proyectoitsv/2025_EWHRA/Diseño/Maqueta PMV/Dispositivo EWHRA (Conjunto).jpg

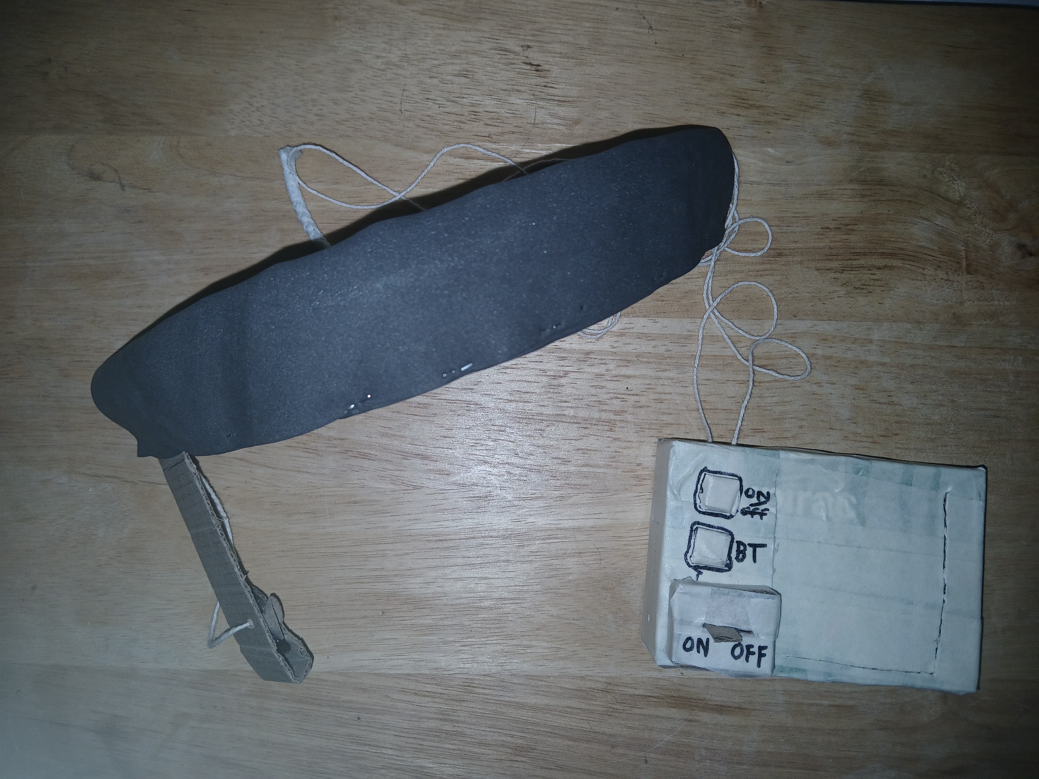
Diseño/Maqueta PMV/Dispositivo EWHRA (Conjunto).jpg
