proyectoitsv/2025_EWHRA/Diseño/Maqueta PMV/Usuario con EWHRA (Perfil).jpg

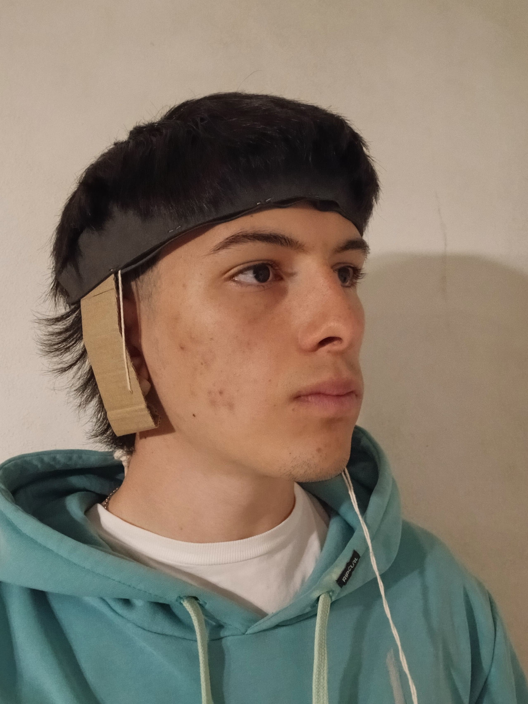
Diseño/Maqueta PMV/Usuario con EWHRA (Perfil).jpg
