proyectoitsv/2025_EWHRA/Diseño/Prototipo PMV/EWHRA_PMV.jpg

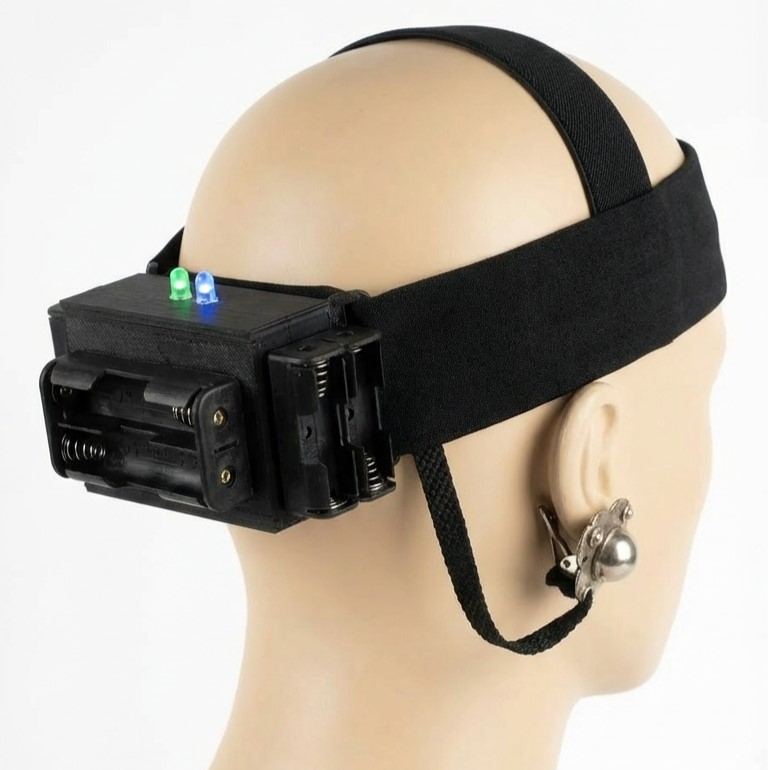
Diseño/Prototipo PMV/EWHRA_PMV.jpg
