proyectoitsv/2025_EWHRA/Diseño/Referencias/1.Alimentacion.png

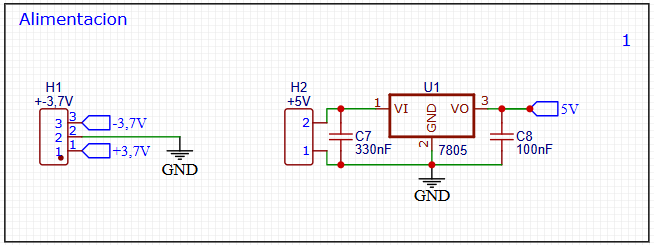
Diseño/Referencias/1.Alimentacion.png
