proyectoitsv/2025_EWHRA/Diseño/Referencias/3.Filtro_pasabanda.png

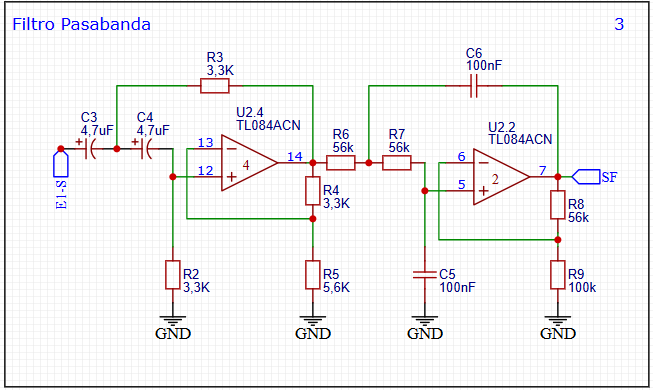
Diseño/Referencias/3.Filtro_pasabanda.png
