proyectoitsv/2025_EWHRA/Diseño/Referencias/4.Amplificador.png

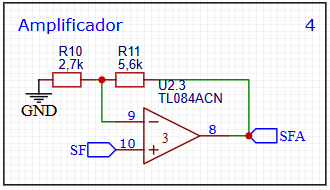
Diseño/Referencias/4.Amplificador.png
