proyectoitsv/2025_EWHRA/Diseño/Referencias/5.Amplificacion_INA.png

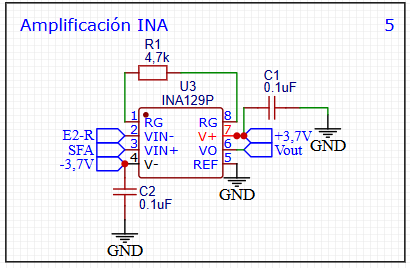
Diseño/Referencias/5.Amplificacion_INA.png
