proyectoitsv/2025_EWHRA/Diseño/Referencias/6.Microcontrolador.png

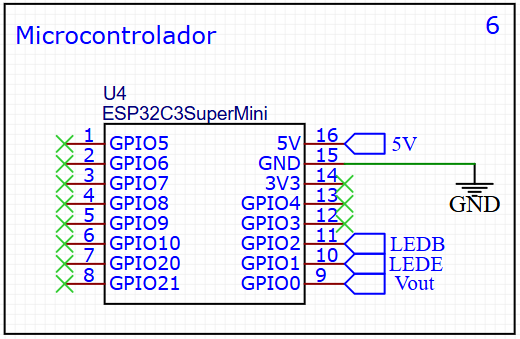
Diseño/Referencias/6.Microcontrolador.png
