proyectoitsv/2025_EWHRA/Interfaz Gráfica/Screenshots/AppEWHRA_Conectado.jpg

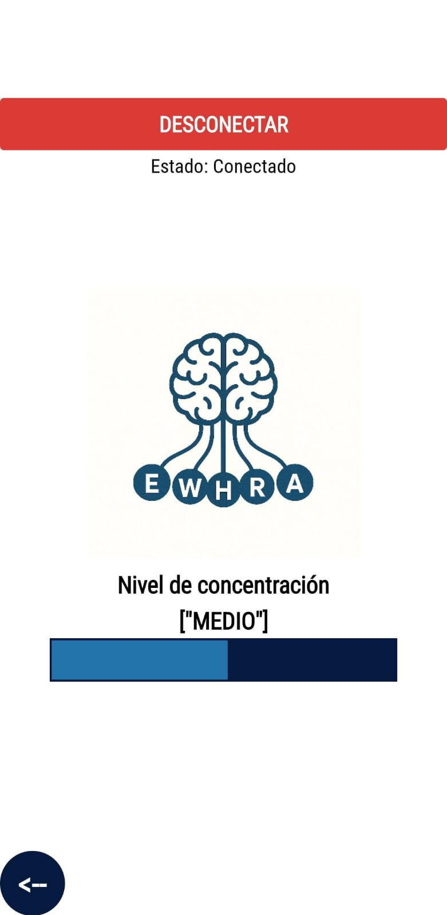
Interfaz Gráfica/Screenshots/AppEWHRA_Conectado.jpg
