proyectoitsv/2025_EWHRA/Interfaz Gráfica/Screenshots/AppEWHRA_Desconectado.jpg

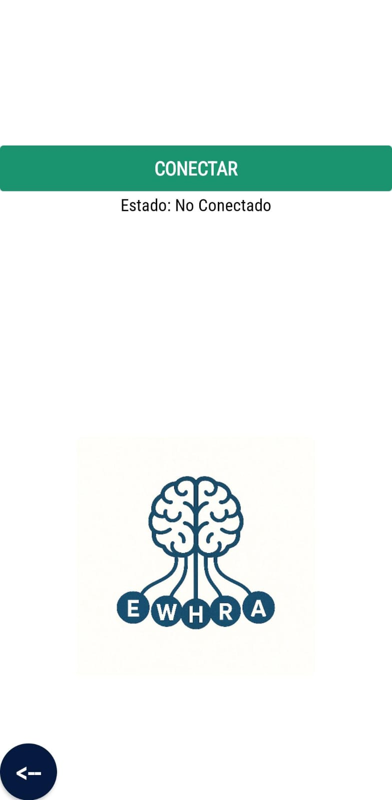
Interfaz Gráfica/Screenshots/AppEWHRA_Desconectado.jpg
