proyectoitsv/2025_EWHRA/Interfaz Gráfica/Screenshots/AppEWHRA_Inicio.jpg

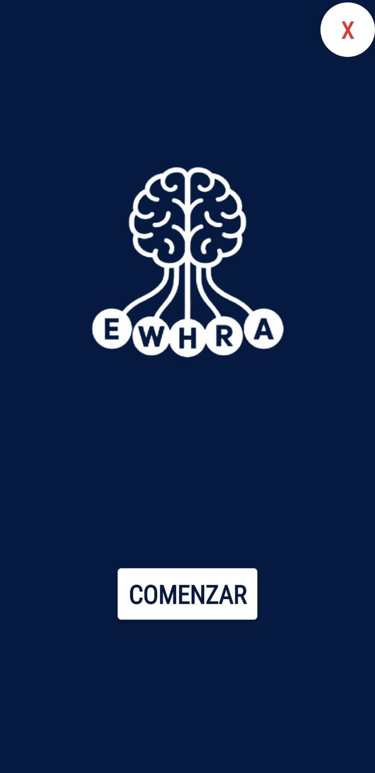
Interfaz Gráfica/Screenshots/AppEWHRA_Inicio.jpg
